Duke-Axer/can_t_board/ltSpice/Power_supply.asc

C1: cap; 0.1µ; V=6.3 Irms=0 Rser=0 Lser=0 mfg="Murata" pn="GRM033R60J123KE01" type="X5R"
C2: cap; 0.1µ; V=25 Irms=0 Rser=0.037 Lser=674p mfg="Würth Elektronik" pn="885012210008 WCAP-CSGP 1812" type="X7R"
C3: cap; 4700µ; V=6.3 Irms=1.73 Rser=0.034 Lser=0 mfg="Panasonic" pn="ECA0JFQ472" type="Al electrolytic"
C4: cap; 1µ; V=10 Irms=0 Rser=0.0078 Lser=250p mfg="Würth Elektronik" pn="885012207022 WCAP-CSGP 0805" type="X7R"
C5: cap; 10µ; V=4 Irms=0 Rser=0 Lser=0 mfg="Murata" pn="GRM185R60G106ME15" type="X5R"
D1: diode; 1N4148
D2: diode; 1N4148
D3: diode; 1N4148
D4: diode; 1N4148
L1: ind2; 10h
L2: ind2; 27m
R1: res; 40.2; tol=1 pwr=0.1
R2: res; 1m
R3: res; 30.1; tol=1 pwr=0.1
R4: res; 2K
R5: res; 3.01K; tol=1 pwr=0.1
R8: res; 357; tol=1 pwr=0.1
R9: res; 1k
U1: LT317A
U2: LT1117
V1: voltage; SINE(0  325.27 50)
Named nets: 0, 5_V, 3.3_V
.tran 0 0.5 0 0.001
K L1 L2 0.95
Odbiornik_1
Odbiornik_2
